enphase/interlock-controller/docs/wiring.kicad_sch

## KiCad design docs/wiring.kicad_sch (2026-05-06)

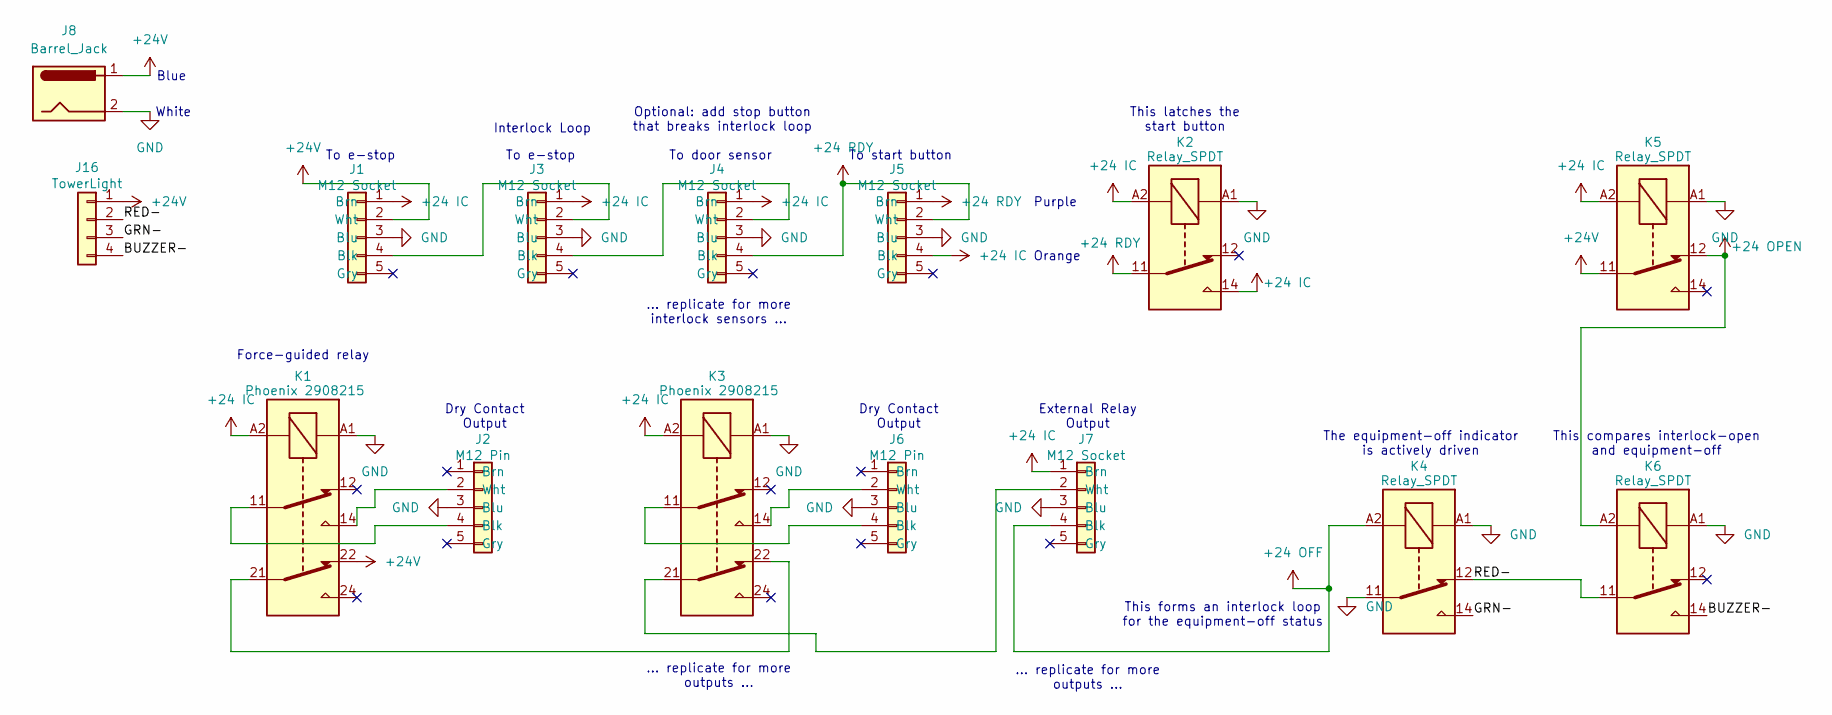
[picture p9: schematic wiring.kicad_sch]

Parts:
J1, J3, J4, J5, J7: M12 Socket
J2, J6: M12 Pin
J8: Barrel_Jack
J16: TowerLight
K1, K3: Phoenix 2908215
K2, K4, K5, K6: Relay_SPDT

Connections:
+24 IC: J1.1 (Brn), J3.1 (Brn), J4.1 (Brn), J5.4 (Blk), J7.1 (Brn), K1.A2, K2.14, K2.A2, K3.A2, K5.A2
+24 OFF: J7.4 (Blk), K4.A2
+24 OPEN: K5.12, K6.A2
+24 RDY: J4.4 (Blk), J5.1 (Brn), J5.2 (Wht), K2.11
+24V: J1.2 (Wht), J8.1, J16.1, K1.22, K5.11
BUZZER-: J16.4, K6.14
GND: J1.3 (Blu), J2.3 (Blu), J3.3 (Blu), J4.3 (Blu), J5.3 (Blu), J6.3 (Blu), J7.3 (Blu), J8.2, K1.A1, K2.A1, K3.A1, K4.11, K4.A1, K5.A1, K6.A1
GRN-: J16.3, K4.14
unnamed: J1.4 (Blk), J3.2 (Wht)
unnamed: J2.2 (Wht), K1.14
unnamed: J2.4 (Blk), K1.11
unnamed: J3.4 (Blk), J4.2 (Wht)
unnamed: J6.2 (Wht), K3.14
unnamed: J6.4 (Blk), K3.11
unnamed: J7.2 (Wht), K3.21
unnamed: K1.21, K3.22
RED-: J16.2, K4.12, K6.11

Notes on the sheet:
Interlock Loop
To e-stop
... replicate for more outputs ...
This compares interlock-open and equipment-off
White
Orange
This latches the start button
The equipment-off indicator is actively driven
Optional: add stop button that breaks interlock loop
To start button
Dry Contact Output
... replicate for more interlock sensors ...
This forms an interlock loop for the equipment-off status
Blue
Force-guided relay
External Relay Output
Purple
To door sensor
